sparkfun/THAT_1206_Breakout/Hardware/tests/input-clamps.asc

D1: diode; 1N4148
D2: diode; 1N4148
D3: zener; EDZV12B
D4: zener; EDZV12B
R1: res; 1k
V1: voltage; 3
V2: voltage; 3
V3: voltage; PULSE(0 25 1 1p 1p .01 .1)
Named nets: 0
.tran 4
